MikeEckels/WS2812B-StarTopper/src/OTAHandler.h

//#pragma once
//#include "Arduino.h"
//#include <WiFiUdp.h>
//#include <ArduinoOTA.h>
//#include <ESP8266WiFi.h>
//#include <ESP8266mDNS.h>
//#include <TelnetStream.h>
//
//class UpdateHandler {
//private:
//    //None
//public:
//    void SetupOTA(const char* hostName, const char* ssid, const char* password);
//    void handle();
//};
